Miq1/FredBoard/Center Panel Mod/AmberDisplay.png

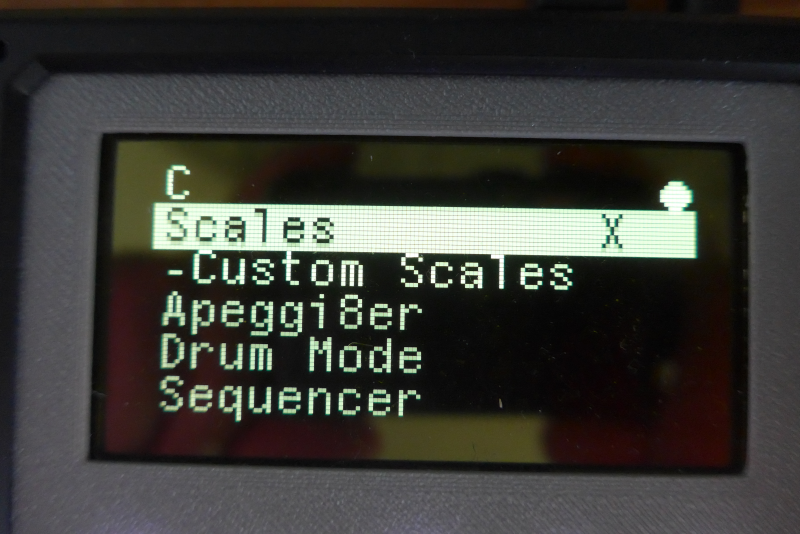
Center Panel Mod/AmberDisplay.png
