Miq1/FredBoard/Center Panel Mod/Finished.png

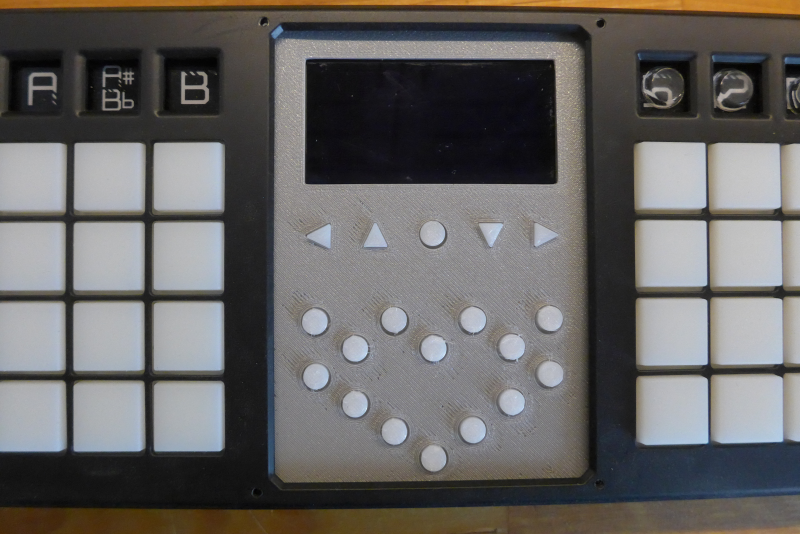
Center Panel Mod/Finished.png
