Miq1/FredBoard/Center Panel Mod/MeltIn1.png

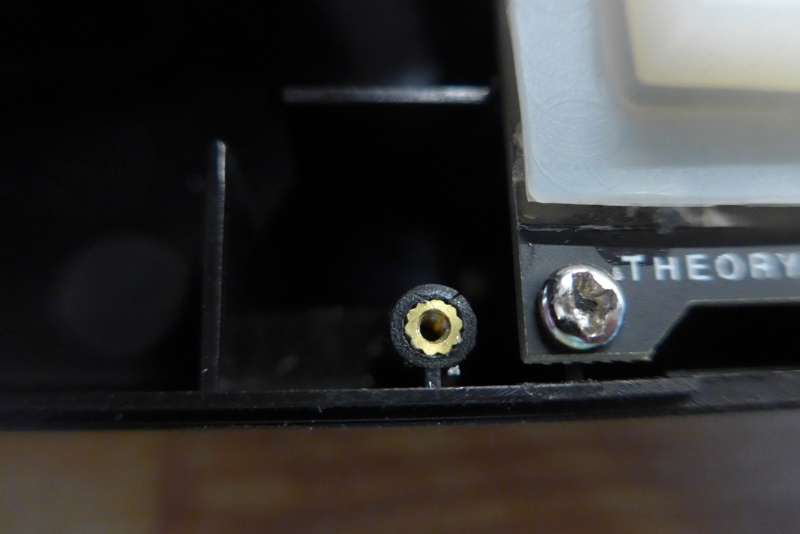
Center Panel Mod/MeltIn1.png
