Miq1/FredBoard/Center Panel Mod/Screen.png

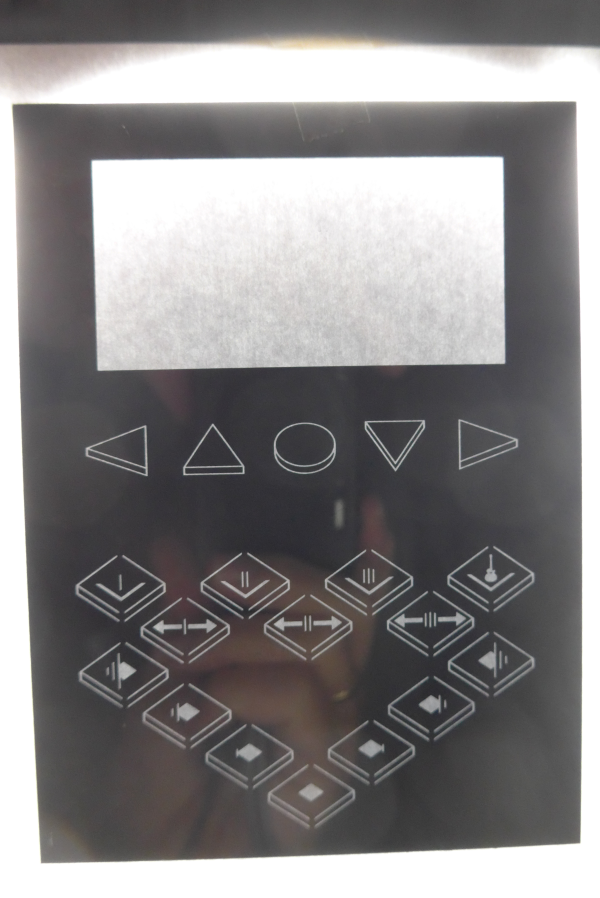
Center Panel Mod/Screen.png
