Miq1/FredBoard/LED-Buttons Mod/Pictures/3WireConnection.png

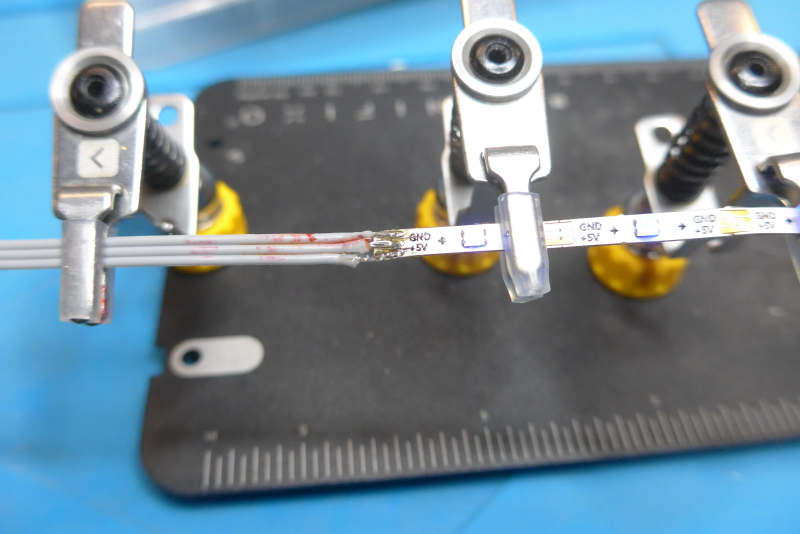
LED-Buttons Mod/Pictures/3WireConnection.png
