Miq1/FredBoard/LED-Buttons Mod/Pictures/ButtonsLit2ndText.png

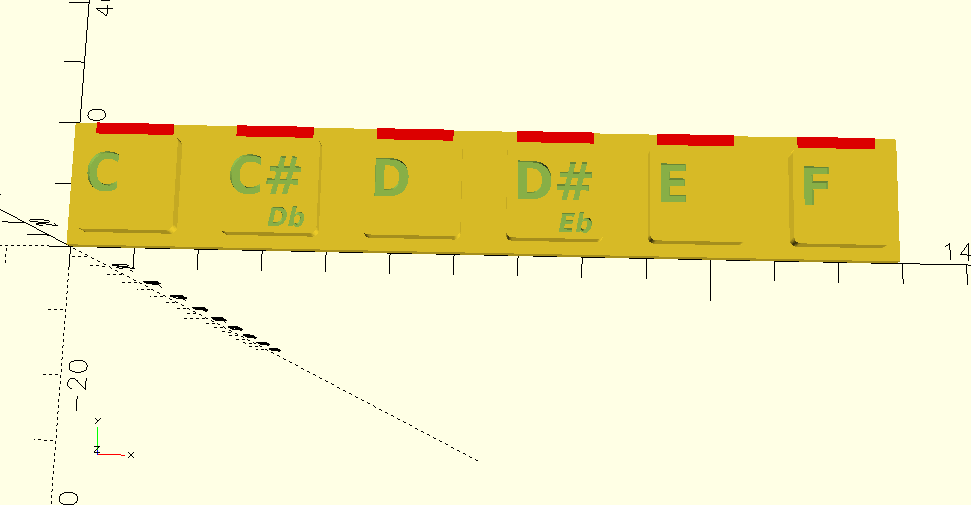
LED-Buttons Mod/Pictures/ButtonsLit2ndText.png
