Miq1/FredBoard/LED-Buttons Mod/Pictures/ButtonsPlain.png

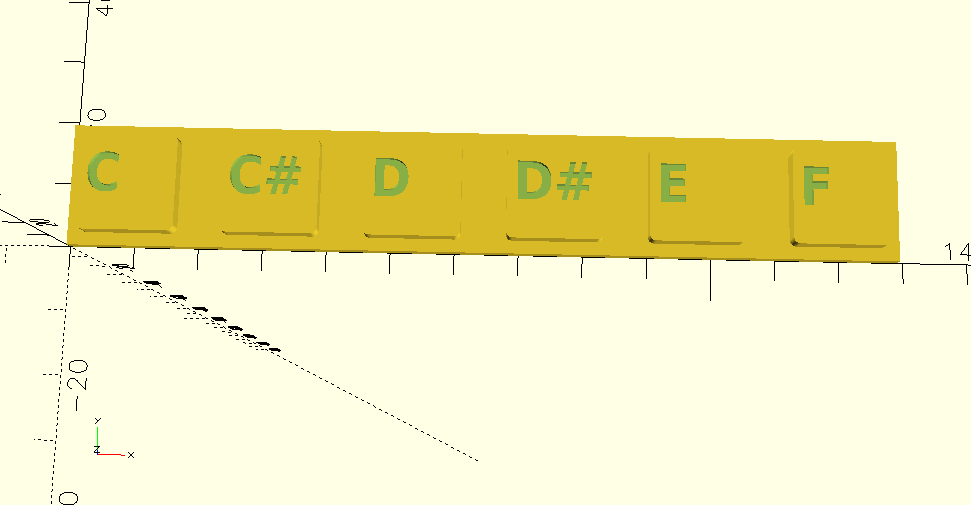
LED-Buttons Mod/Pictures/ButtonsPlain.png
