Miq1/FredBoard/LED-Buttons Mod/Pictures/LEDfixedPin.png

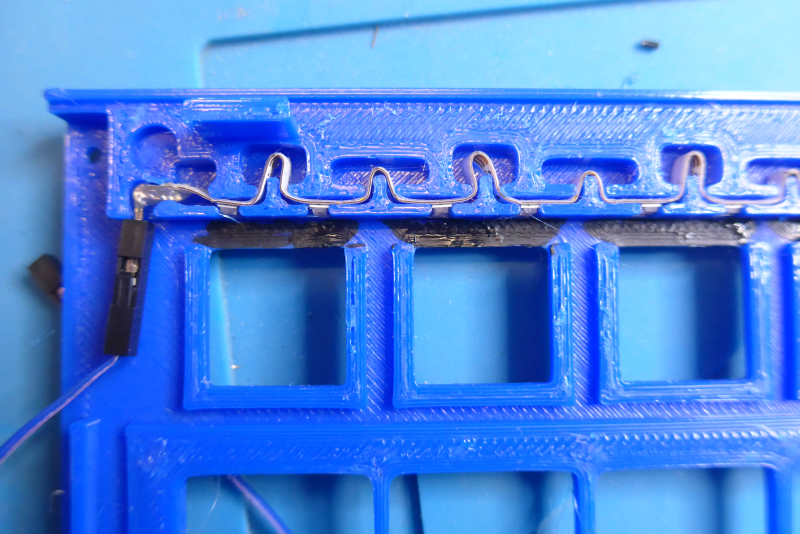
LED-Buttons Mod/Pictures/LEDfixedPin.png
