Miq1/FredBoard/LED-Buttons Mod/Pictures/PartJoins.png

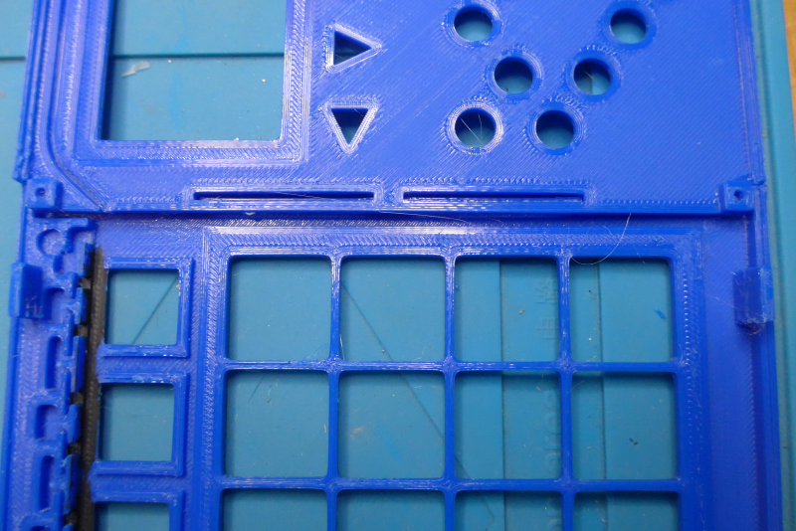
LED-Buttons Mod/Pictures/PartJoins.png
