Miq1/FredBoard/Velostat-Mod/3McutStripe.png

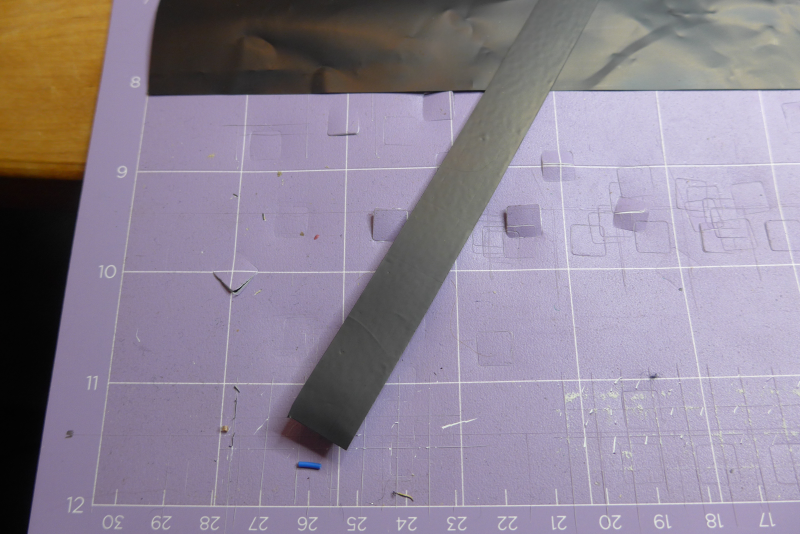
Velostat-Mod/3McutStripe.png
