Miq1/FredBoard/Velostat-Mod/3Mlaminated.png

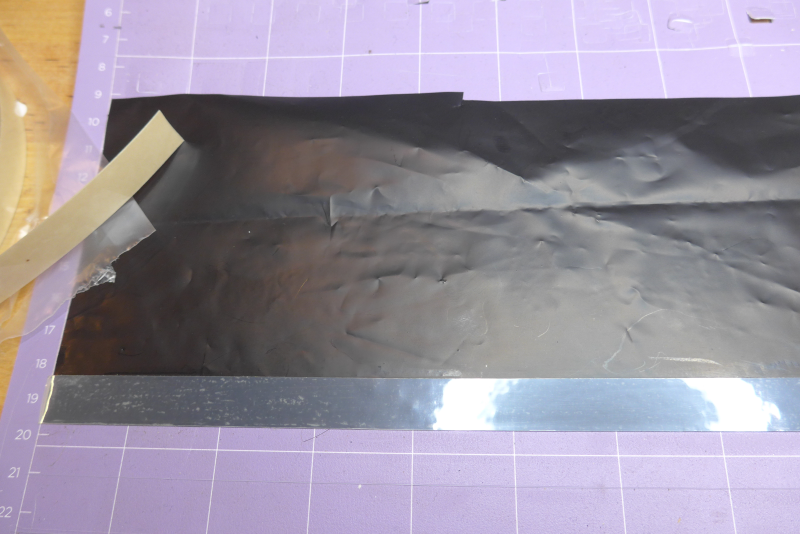
Velostat-Mod/3Mlaminated.png
