Miq1/FredBoard/Velostat-Mod/BumperCut.jpg

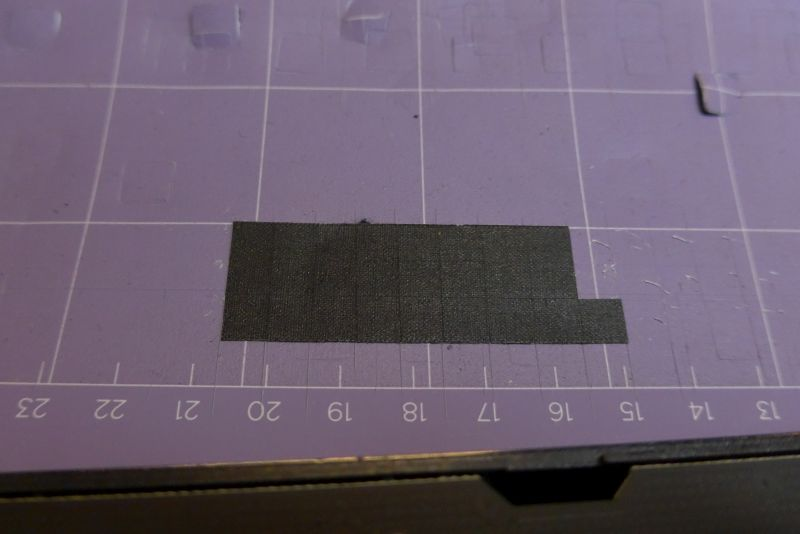
Velostat-Mod/BumperCut.jpg
