Miq1/FredBoard/Velostat-Mod/CarpetTape.jpg

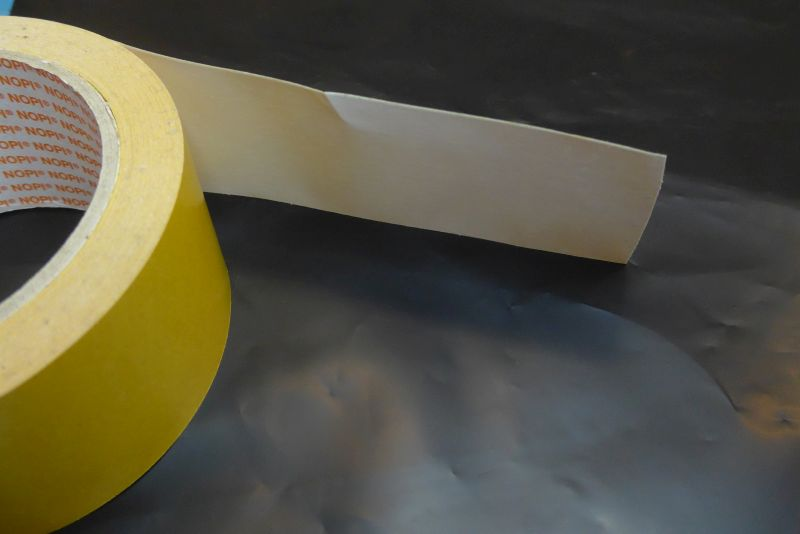
Velostat-Mod/CarpetTape.jpg
