Miq1/FredBoard/Velostat-Mod/CutBench.png

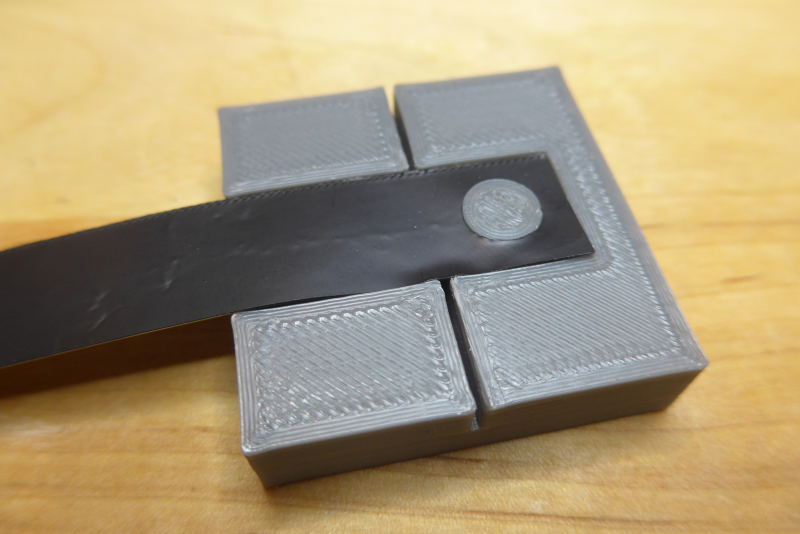
Velostat-Mod/CutBench.png
