Miq1/FredBoard/Velostat-Mod/StickOn.jpg

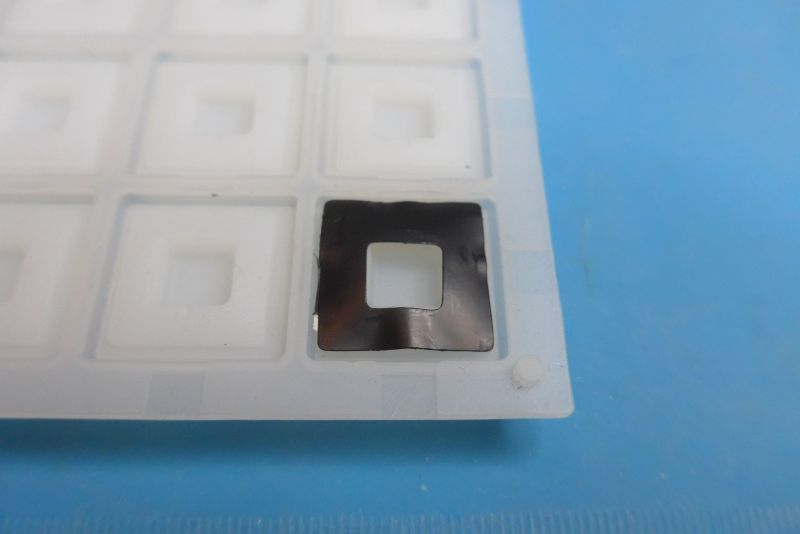
Velostat-Mod/StickOn.jpg
