Miq1/FredBoard/Velostat-Mod/Velostat.png

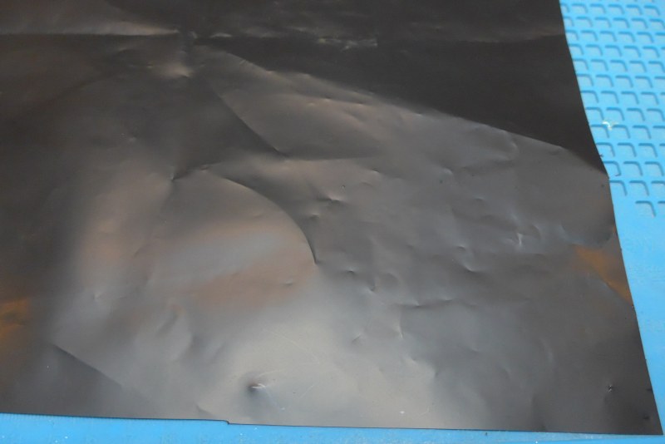
Velostat-Mod/Velostat.png
