Miq1/FredBoard/Top Row Mod/Basic buttons STL/F#-B_Letters_basic.stl

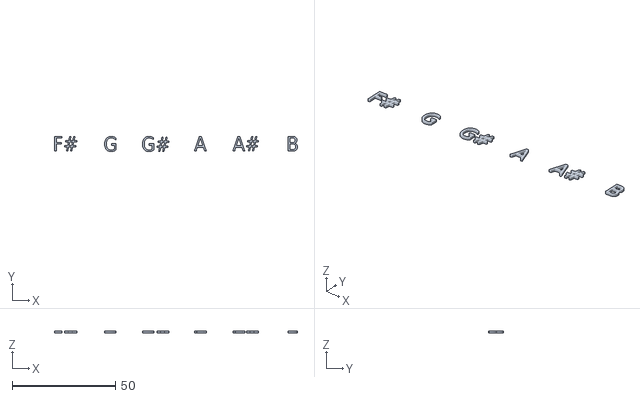
[picture p107: CAD file, 2024-10-12]
Top Row Mod/Basic buttons STL/F#-B_Letters_basic.stl
117.7 x 7.36 x 1.00
