Miq1/FredBoard/LED-Buttons Mod/3D STLs/ButtonsLitC_F2nd.stl

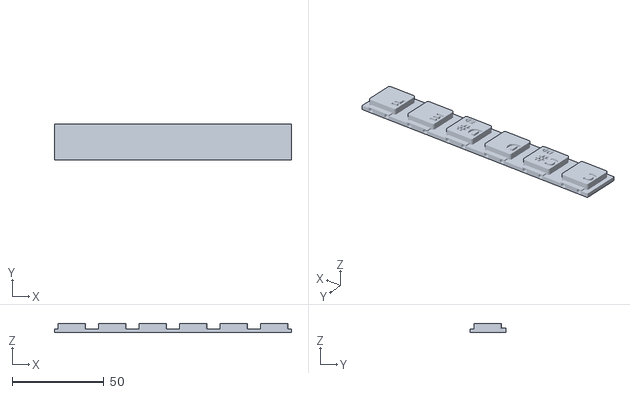
[picture p108: CAD file, 2025-01-05]
LED-Buttons Mod/3D STLs/ButtonsLitC_F2nd.stl
129.0 x 19.4 x 5.00
