Miq1/FredBoard/Top Row Mod/Basic buttons STL/M1-M7_Letters_basic.stl

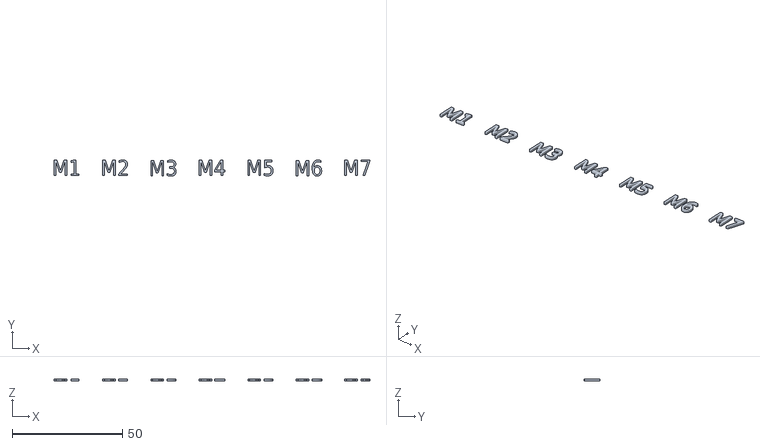
[picture p109: CAD file, 2024-10-12]
Top Row Mod/Basic buttons STL/M1-M7_Letters_basic.stl
143.5 x 7.42 x 1.00
