Miq1/FredBoard/LED-Buttons Mod/3D STLs/LettersLitIo_Do2nd.stl

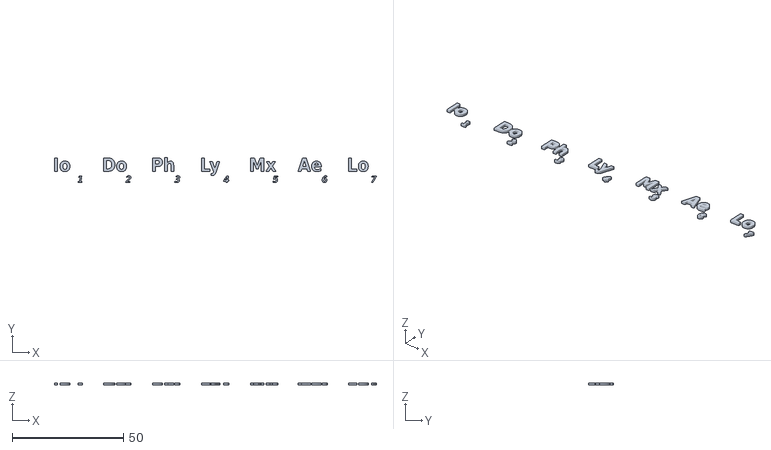
[picture p110: CAD file, 2025-01-05]
LED-Buttons Mod/3D STLs/LettersLitIo_Do2nd.stl
144.6 x 11.4 x 1.10
