Miq1/FredBoard/Top Row Mod/Basic buttons STL/U1-U3_Buttons_basic.stl

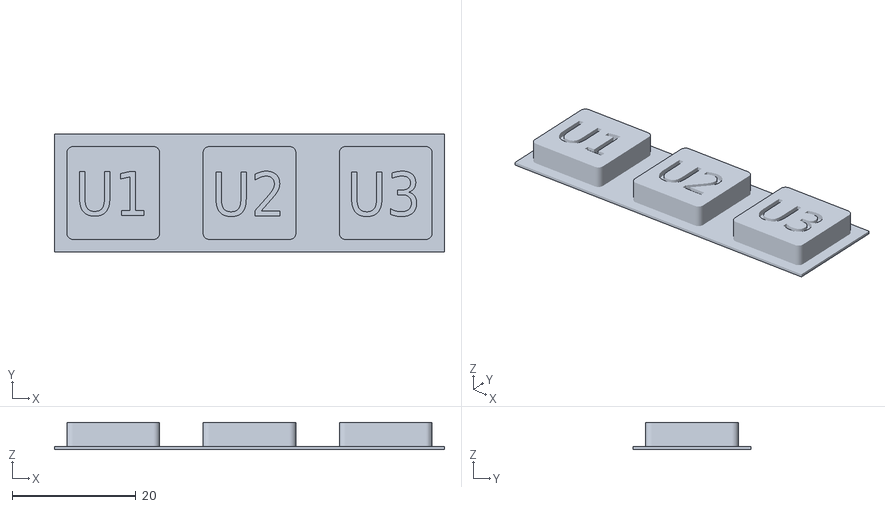
[picture p111: CAD file, 2024-10-12]
Top Row Mod/Basic buttons STL/U1-U3_Buttons_basic.stl
63.0 x 19.0 x 4.42
