Miq1/FredBoard/LED-Buttons Mod/3D STLs/ButtonsLitF#_B2nd.stl

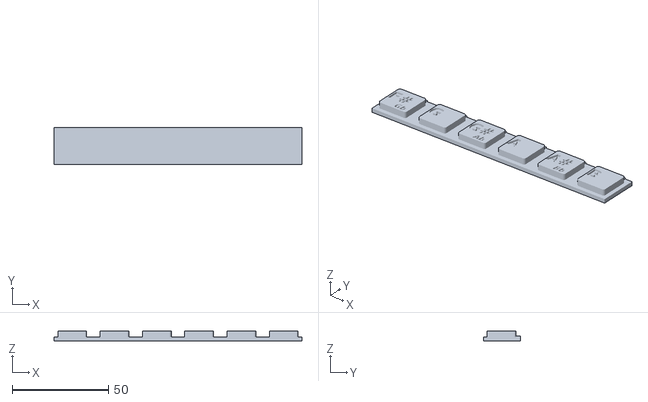
[picture p112: CAD file, 2025-01-05]
LED-Buttons Mod/3D STLs/ButtonsLitF#_B2nd.stl
129.0 x 19.4 x 5.00
