Miq1/FredBoard/Top Row Mod/Basic buttons STL/C-F_Letters_basic.stl

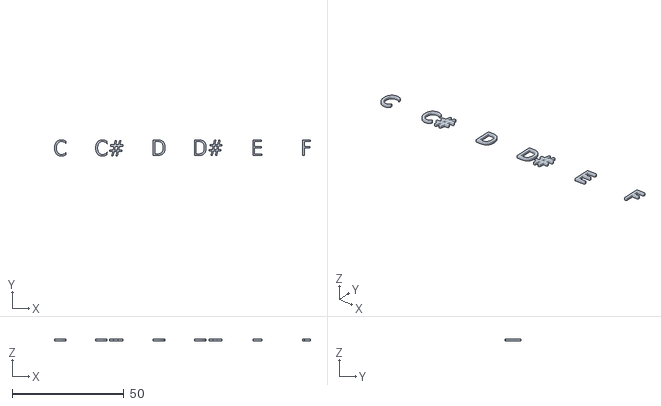
[picture p113: CAD file, 2024-10-12]
Top Row Mod/Basic buttons STL/C-F_Letters_basic.stl
114.8 x 7.36 x 1.00
