Miq1/FredBoard/LED-Buttons Mod/3D STLs/LettersLitC_F2nd.stl

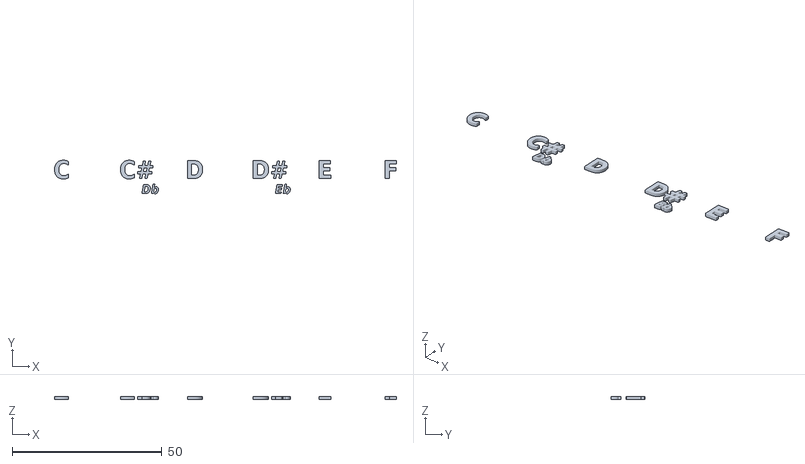
[picture p114: CAD file, 2025-01-05]
LED-Buttons Mod/3D STLs/LettersLitC_F2nd.stl
114.1 x 11.2 x 1.10
