Miq1/FredBoard/LED-Buttons Mod/3D STLs/ButtonsLit5_122nd.stl

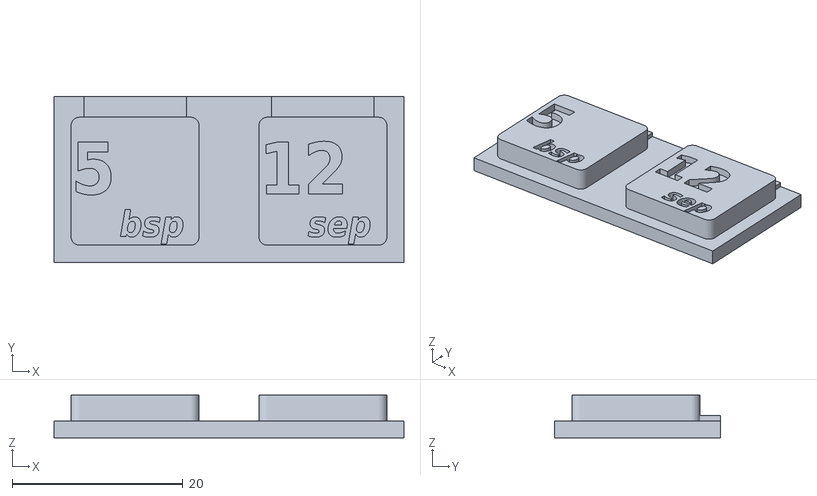
[picture p116: CAD file, 2025-01-05]
LED-Buttons Mod/3D STLs/ButtonsLit5_122nd.stl
41.0 x 19.4 x 5.00
