Miq1/FredBoard/Top Row Mod/Basic buttons STL/M1-M7_Buttons_basic.stl

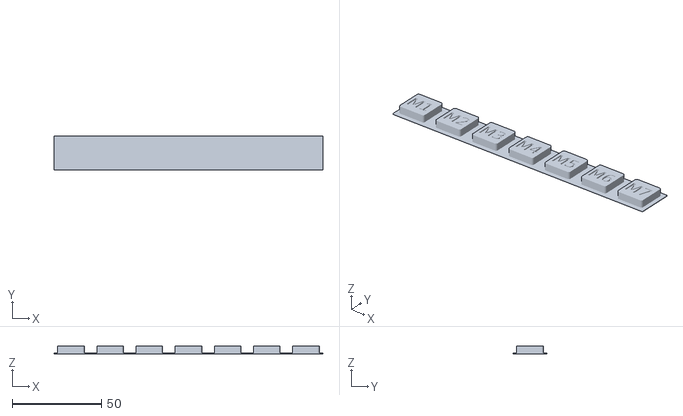
[picture p117: CAD file, 2024-10-12]
Top Row Mod/Basic buttons STL/M1-M7_Buttons_basic.stl
151.0 x 19.0 x 4.42
