Miq1/FredBoard/LED-Buttons Mod/3D STLs/LettersLitU1232nd.stl

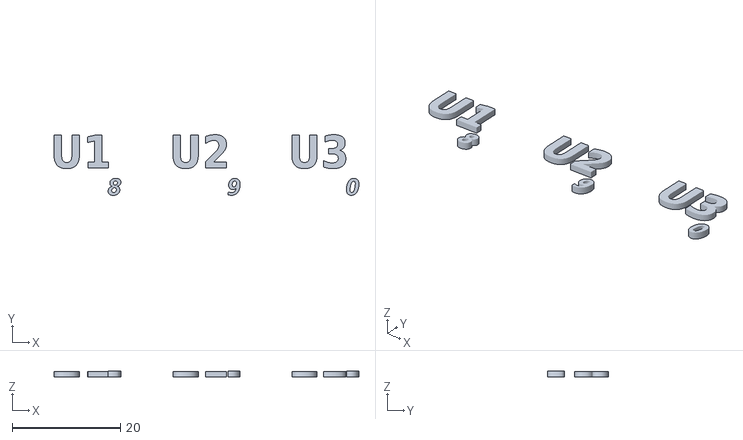
[picture p118: CAD file, 2025-01-05]
LED-Buttons Mod/3D STLs/LettersLitU1232nd.stl
56.4 x 11.2 x 1.10
