Miq1/FredBoard/Top Row Mod/Basic buttons STL/5-12_Letters_basic.stl

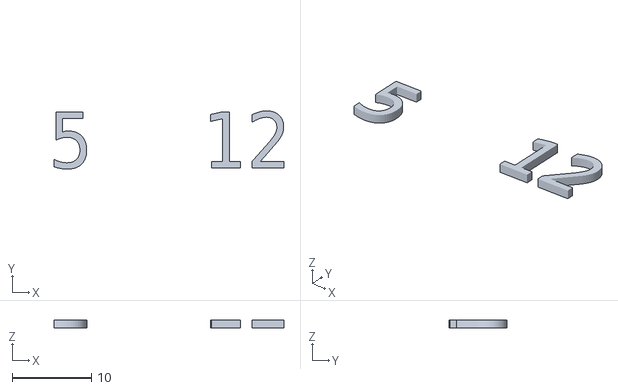
[picture p119: CAD file, 2024-10-12]
Top Row Mod/Basic buttons STL/5-12_Letters_basic.stl
29.0 x 7.36 x 1.00
