Miq1/FredBoard/LED-Buttons Mod/3D STLs/ButtonsLitM1_M72nd.stl

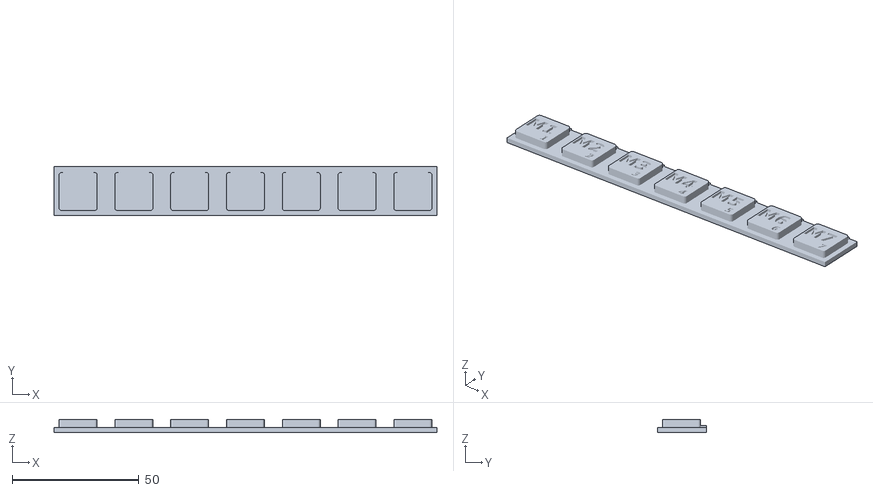
[picture p120: CAD file, 2025-01-05]
LED-Buttons Mod/3D STLs/ButtonsLitM1_M72nd.stl
151.0 x 19.4 x 5.00
