Miq1/FredBoard/Top Row Mod/Basic buttons STL/F#-B_Buttons_basic.stl

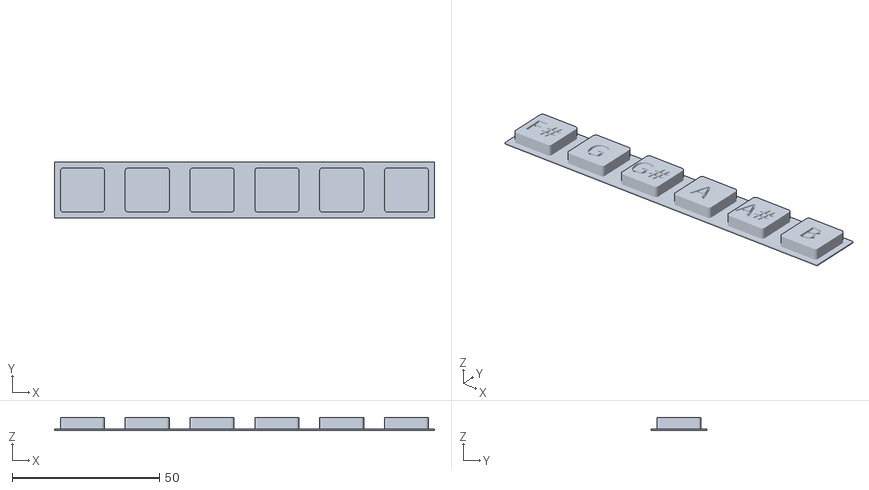
[picture p121: CAD file, 2024-10-12]
Top Row Mod/Basic buttons STL/F#-B_Buttons_basic.stl
129.0 x 19.0 x 4.42
