Miq1/FredBoard/LED-Buttons Mod/3D STLs/LettersLitM1_M72nd.stl

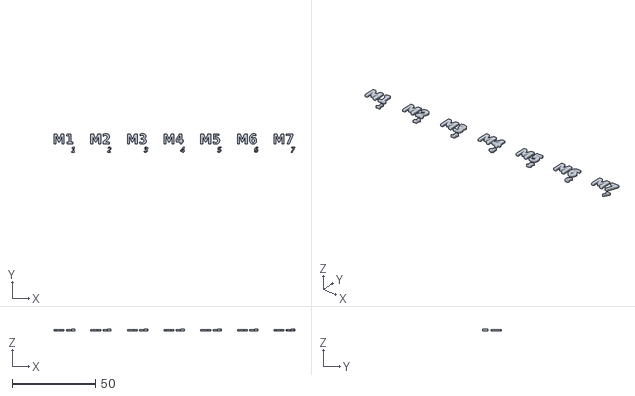
[picture p122: CAD file, 2025-01-05]
LED-Buttons Mod/3D STLs/LettersLitM1_M72nd.stl
144.6 x 11.2 x 1.10
