Miq1/FredBoard/LED-Buttons Mod/3D STLs/LettersLitF#_B2nd.stl

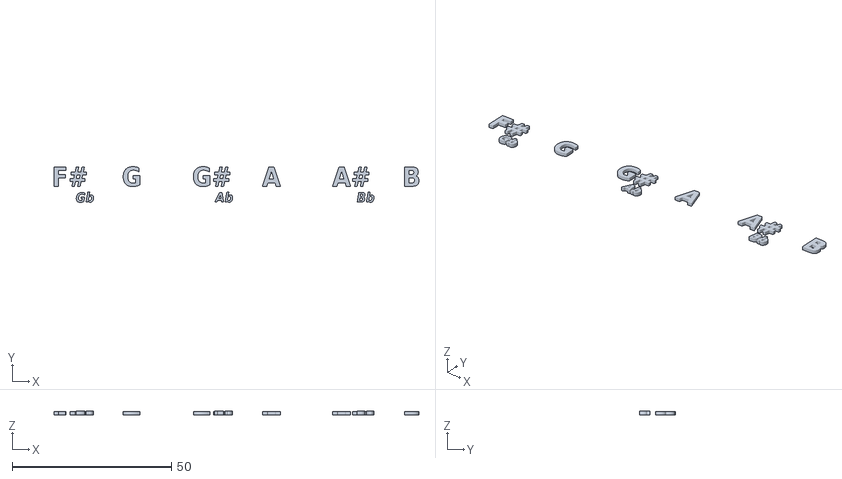
[picture p123: CAD file, 2025-01-05]
LED-Buttons Mod/3D STLs/LettersLitF#_B2nd.stl
114.5 x 11.2 x 1.10
