Miq1/FredBoard/LED-Buttons Mod/3D STLs/LettersLit5_122nd.stl

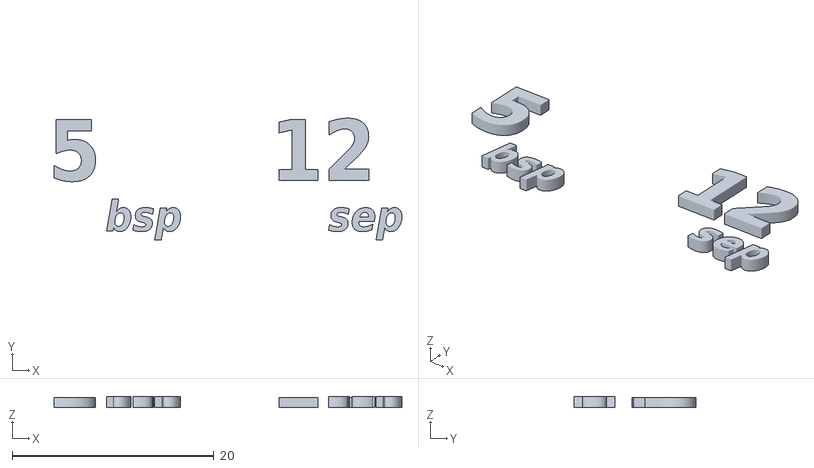
[picture p124: CAD file, 2025-01-05]
LED-Buttons Mod/3D STLs/LettersLit5_122nd.stl
34.5 x 12.1 x 1.10
