Miq1/FredBoard/LED-Buttons Mod/3D STLs/ButtonsLitU1232nd.stl

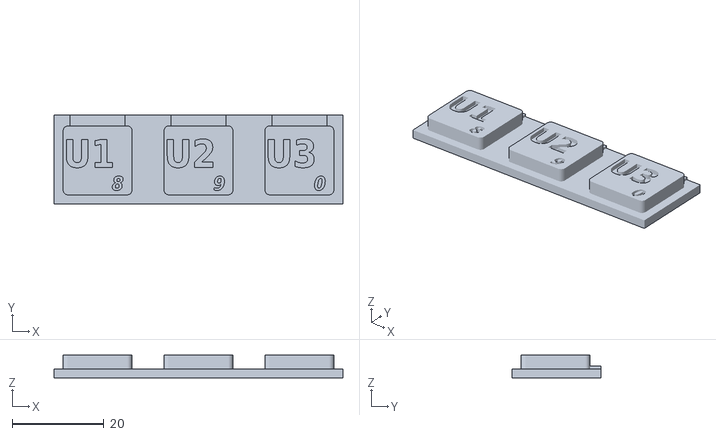
[picture p125: CAD file, 2025-01-05]
LED-Buttons Mod/3D STLs/ButtonsLitU1232nd.stl
63.0 x 19.4 x 5.00
