Miq1/FredBoard/LED-Buttons Mod/3D STLs/ButtonsLitIo_Do2nd.stl

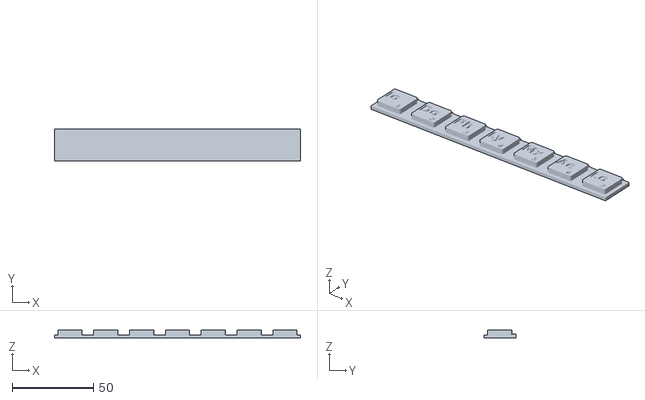
[picture p126: CAD file, 2025-01-05]
LED-Buttons Mod/3D STLs/ButtonsLitIo_Do2nd.stl
151.0 x 19.4 x 5.00
