Miq1/FredBoard/LED-Buttons Mod/3D STLs/PCBsocketSmall.stl

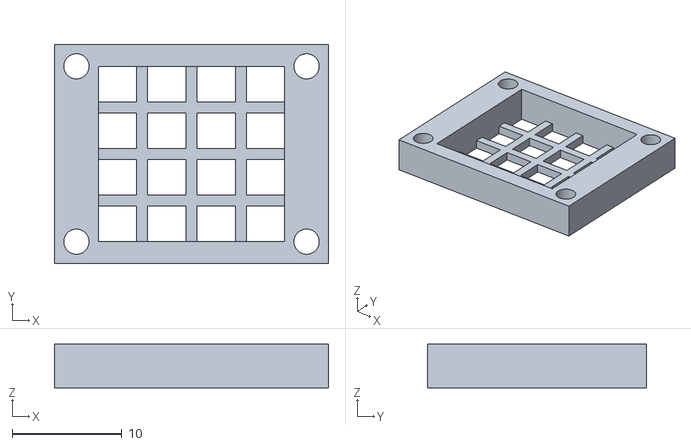
[picture p127: CAD file, 2024-12-27]
LED-Buttons Mod/3D STLs/PCBsocketSmall.stl
25.0 x 20.0 x 4.00
