Miq1/FredBoard/LED-Buttons Mod/3D STLs/PCBsocketLarge.stl

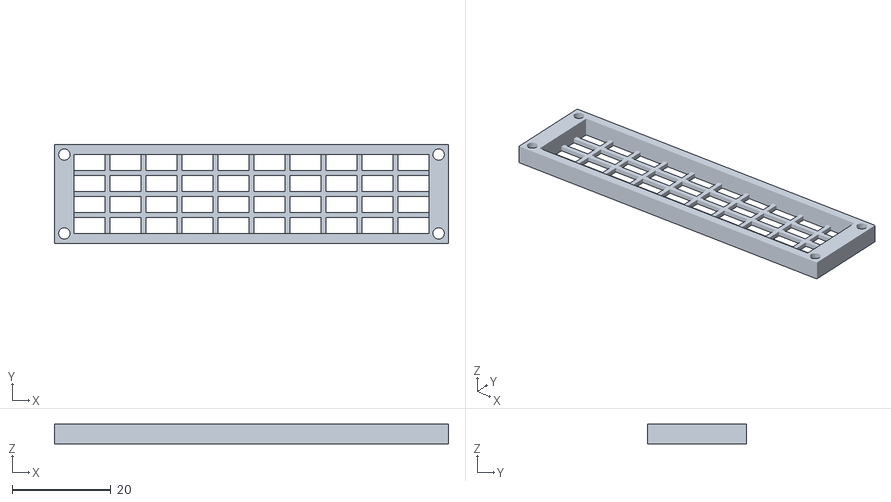
[picture p128: CAD file, 2024-12-27]
LED-Buttons Mod/3D STLs/PCBsocketLarge.stl
80.0 x 20.0 x 4.00
