Miq1/FredBoard/LED-Buttons Mod/3D STLs/BendingTool.stl

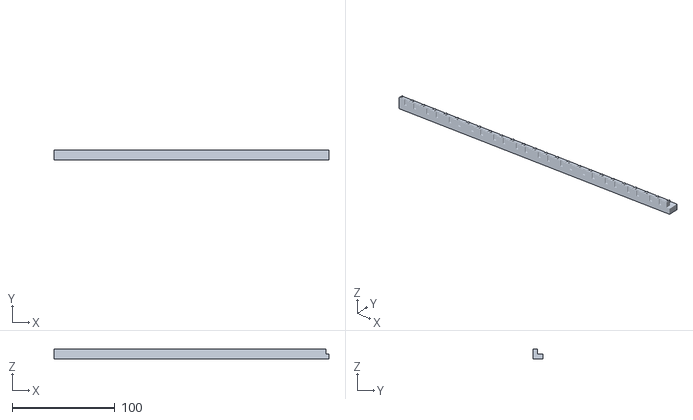
[picture p129: CAD file, 2024-12-27]
LED-Buttons Mod/3D STLs/BendingTool.stl
267.0 x 9.30 x 9.80
