Miq1/FredBoard/LED-Buttons Mod/3D STLs/CableClamp.stl

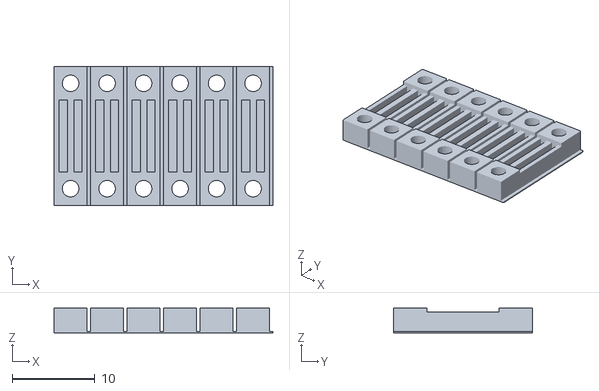
[picture p130: CAD file, 2024-12-27]
LED-Buttons Mod/3D STLs/CableClamp.stl
26.4 x 16.7 x 3.00
