Miq1/FredBoard/LED-Buttons Mod/3D STLs/TB-Parts-Arrow_up_down.stl

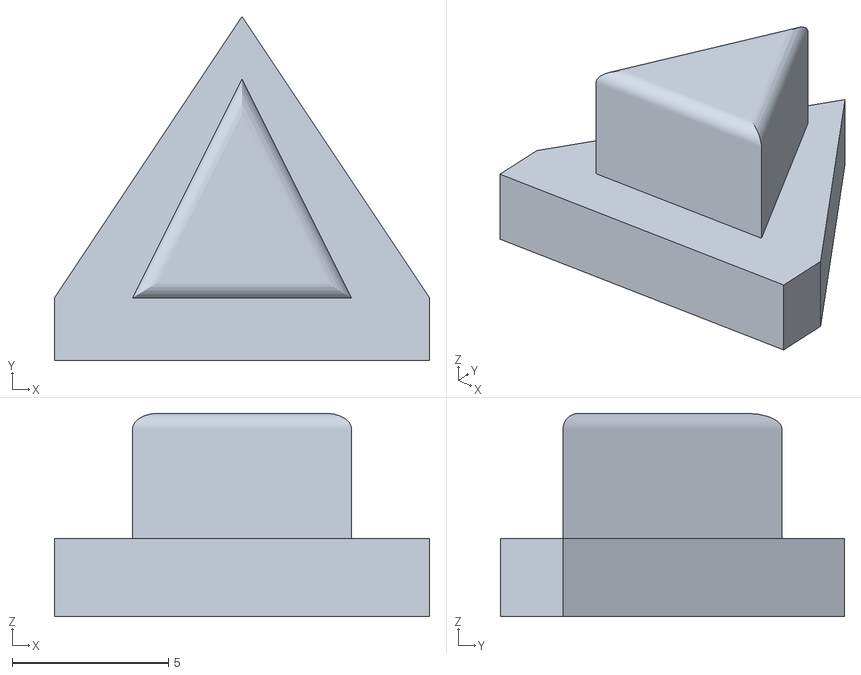
[picture p131: CAD file, 2024-10-01]
LED-Buttons Mod/3D STLs/TB-Parts-Arrow_up_down.stl
12.0 x 11.0 x 6.50
