Miq1/FredBoard/LED-Buttons Mod/3D STLs/TB-Parts-Rhomb.stl

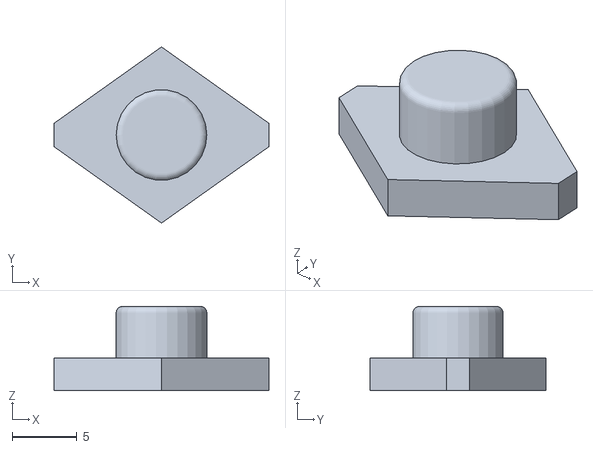
[picture p132: CAD file, 2024-10-01]
LED-Buttons Mod/3D STLs/TB-Parts-Rhomb.stl
16.6 x 13.6 x 6.50
