Miq1/FredBoard/LED-Buttons Mod/3D STLs/TB-Parts-Center.stl

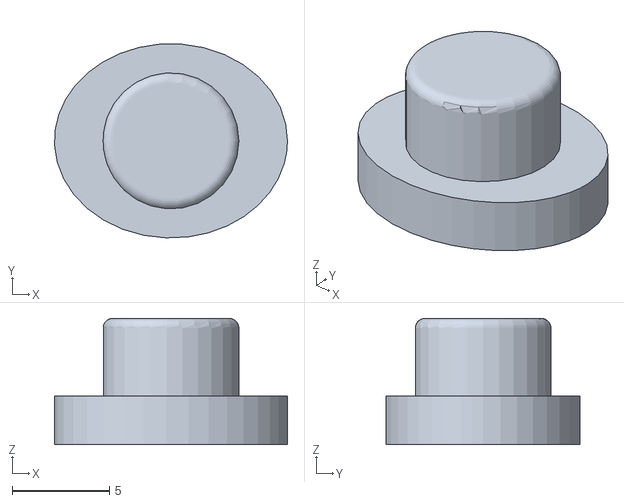
[picture p133: CAD file, 2024-10-01]
LED-Buttons Mod/3D STLs/TB-Parts-Center.stl
12.0 x 9.97 x 6.50
