Miq1/FredBoard/LED-Buttons Mod/3D STLs/TB-Parts-Arrow_Left_Right.stl

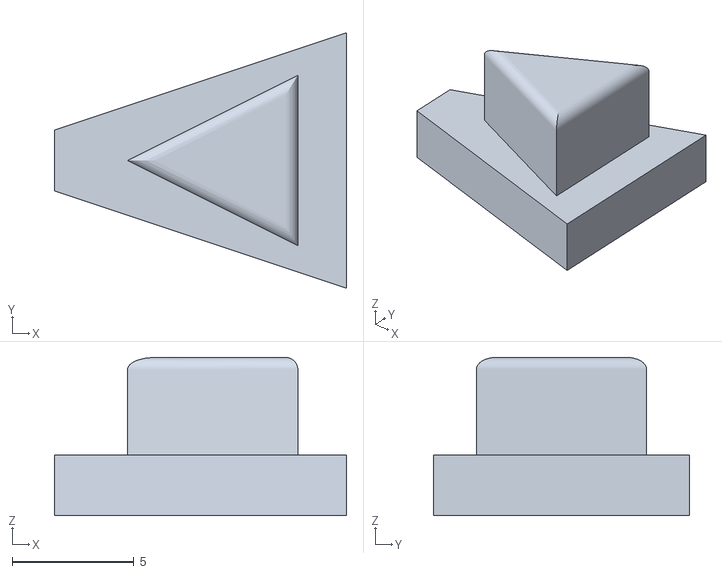
[picture p134: CAD file, 2024-10-01]
LED-Buttons Mod/3D STLs/TB-Parts-Arrow_Left_Right.stl
12.0 x 10.5 x 6.50
